tritoke/keyboard/pcb/wide_paisley.png

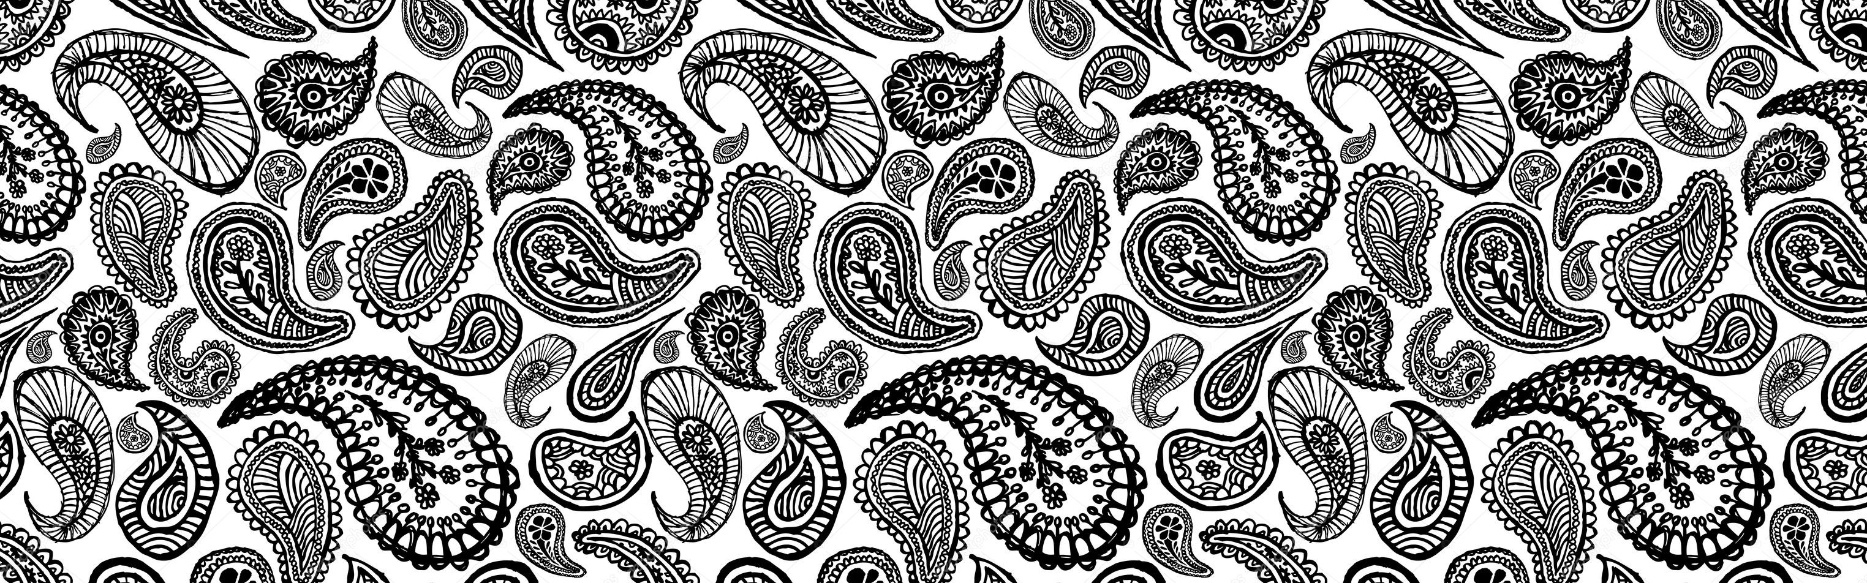
pcb/wide_paisley.png
